WildernessLabs/Clima/Image_Assets/Clima_w_new_Solar_Circuit.jpg

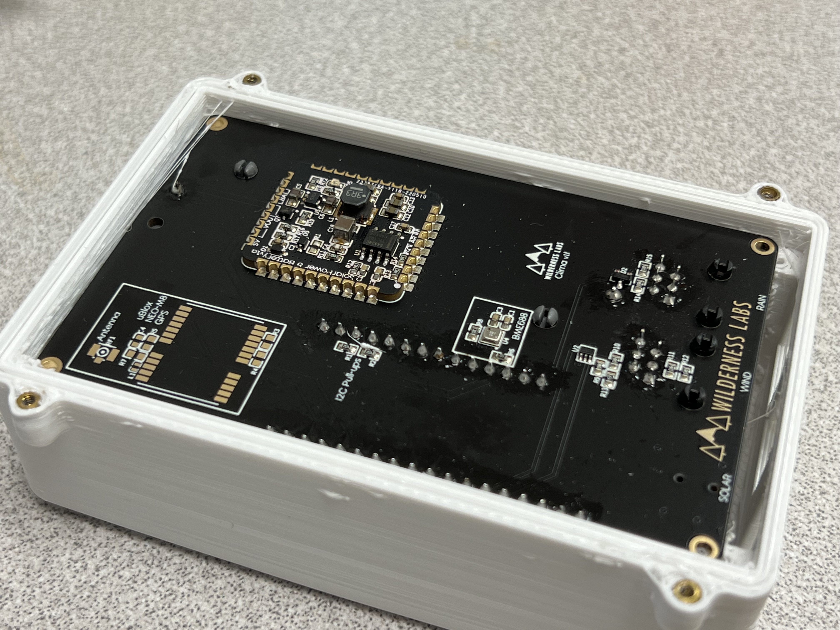
Image_Assets/Clima_w_new_Solar_Circuit.jpg
